antmicro/environment-sensor-myra-baseboard/assets/previews/layer1.png

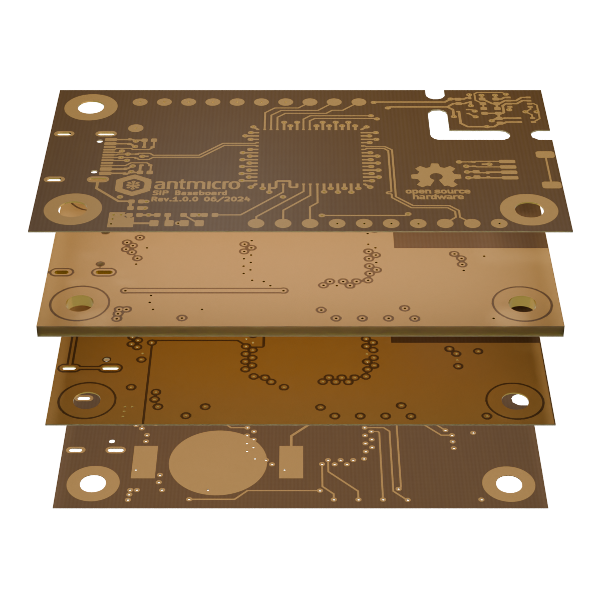
assets/previews/layer1.png
