antmicro/environment-sensor-myra-baseboard/assets/previews/layer2.png

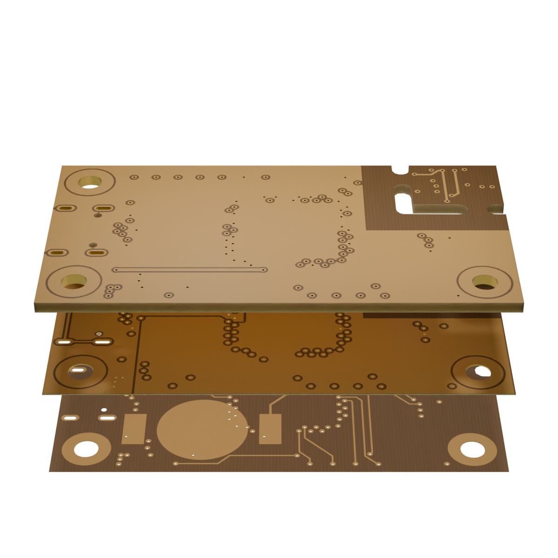
assets/previews/layer2.png
