antmicro/environment-sensor-myra-baseboard/assets/previews/layer3.png

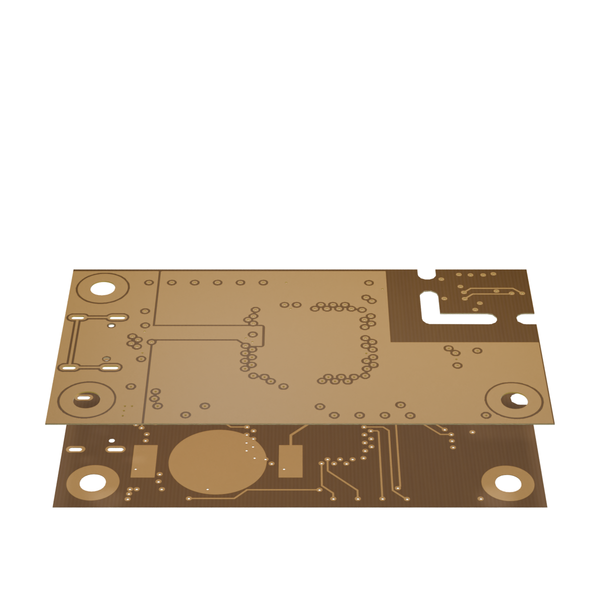
assets/previews/layer3.png
