antmicro/environment-sensor-myra-baseboard/assets/previews/layer4.png

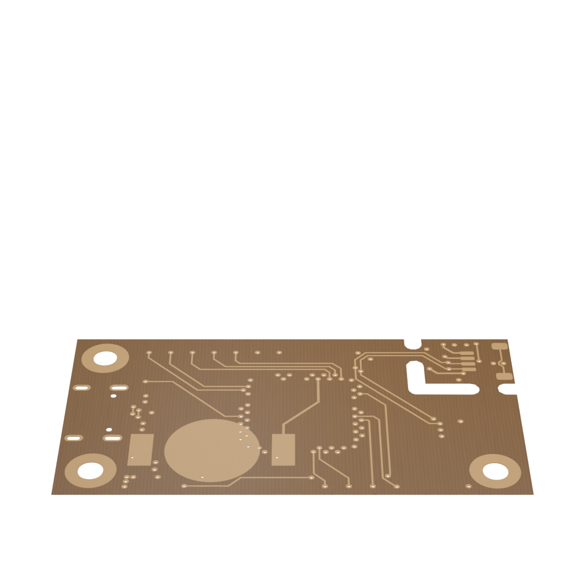
assets/previews/layer4.png
