antmicro/environment-sensor-myra-baseboard/assets/previews/leftB.png

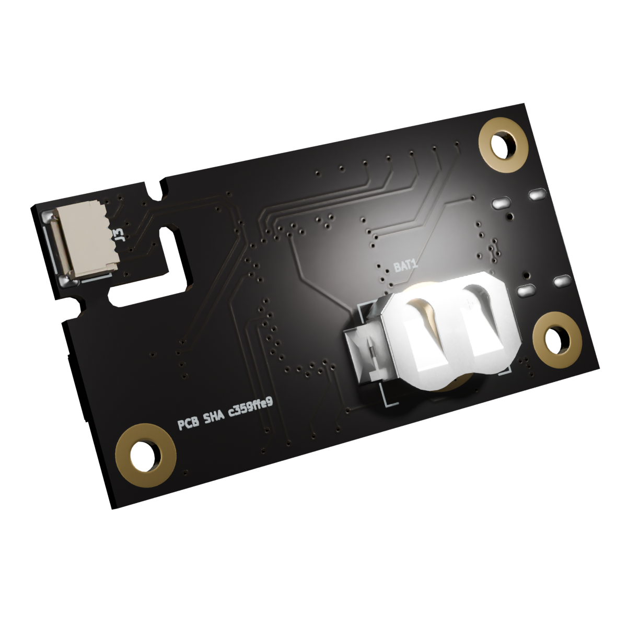
assets/previews/leftB.png
