antmicro/environment-sensor-myra-baseboard/assets/previews/orthoB.png

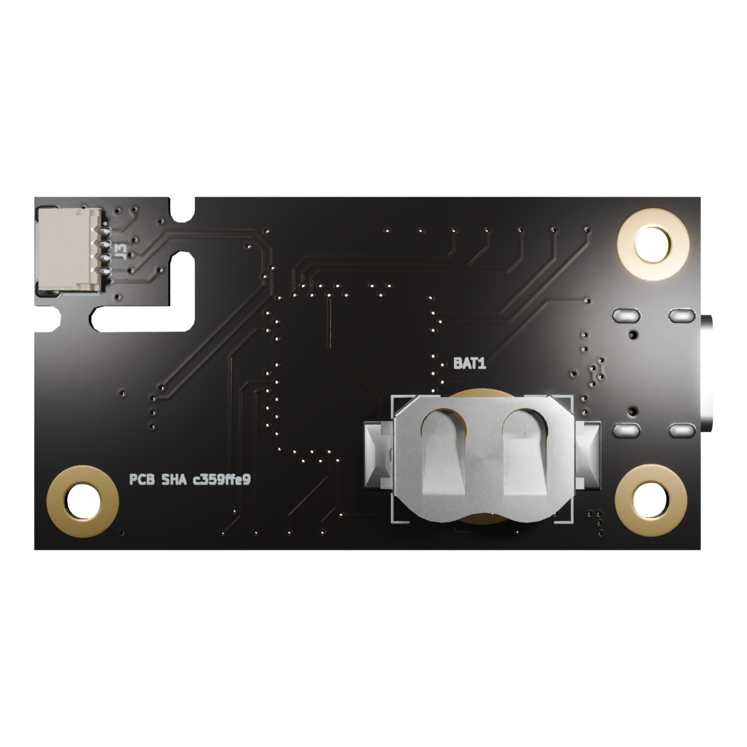
assets/previews/orthoB.png
