antmicro/environment-sensor-myra-baseboard/assets/previews/rightB.png

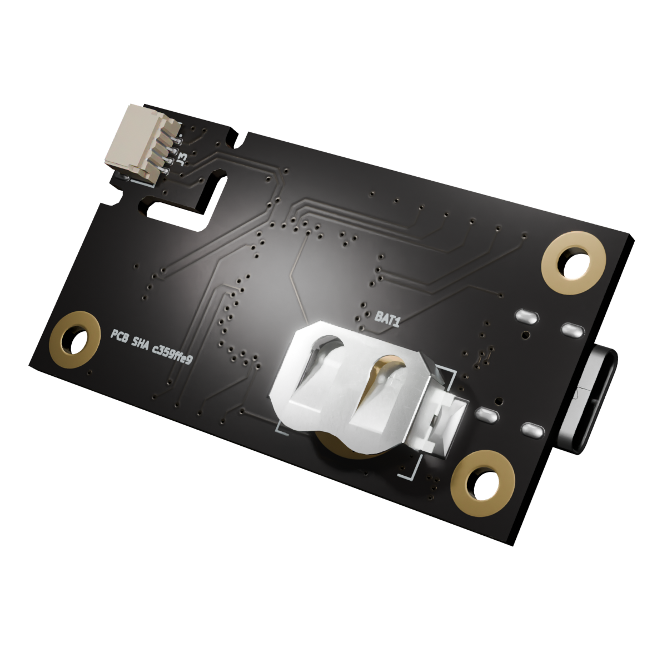
assets/previews/rightB.png
